max-verem/LensRotaryDecoder/HW/Camera_Lens_Cable/images/pic1.png

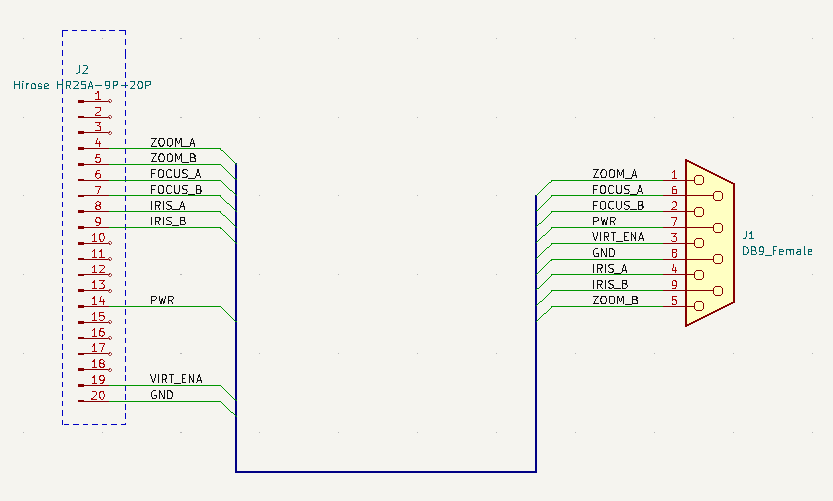
HW/Camera_Lens_Cable/images/pic1.png
