max-verem/LensRotaryDecoder/STM32/Clock_Configuration_16.png

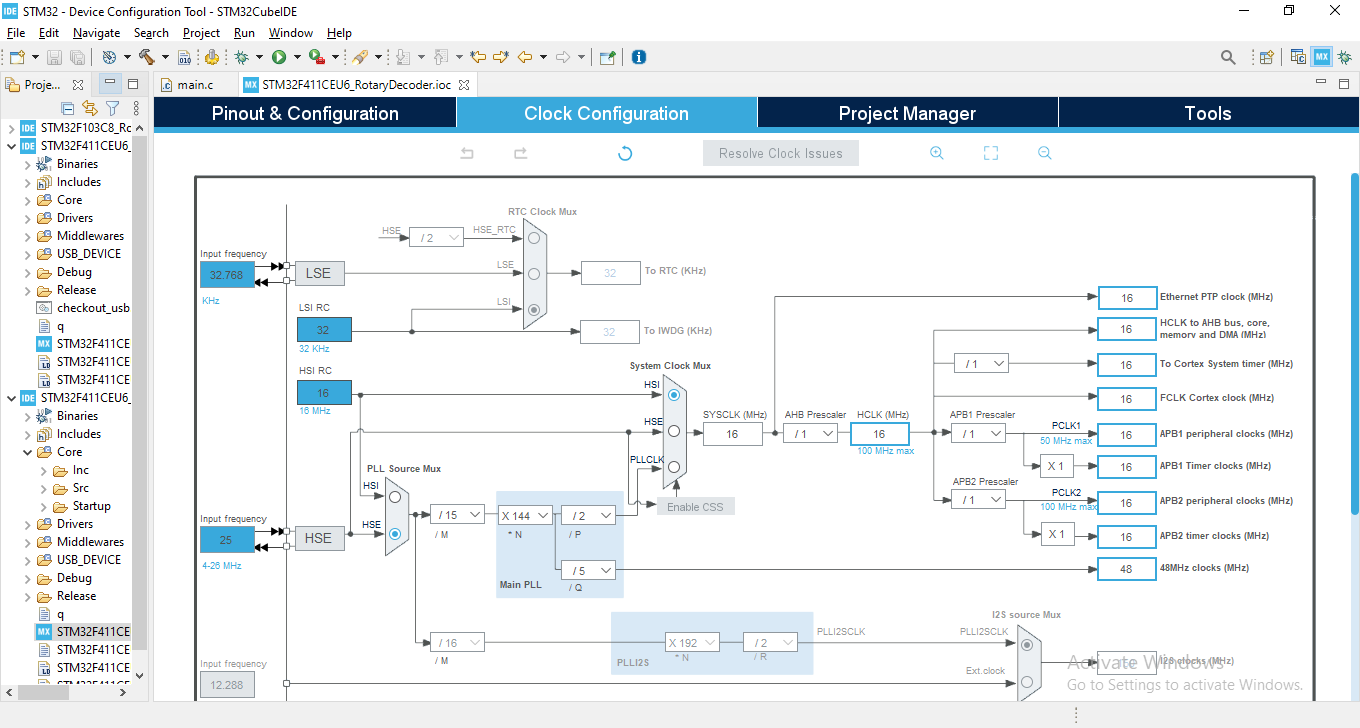
STM32/Clock_Configuration_16.png
