max-verem/LensRotaryDecoder/STM32/STM32F103C8.webp

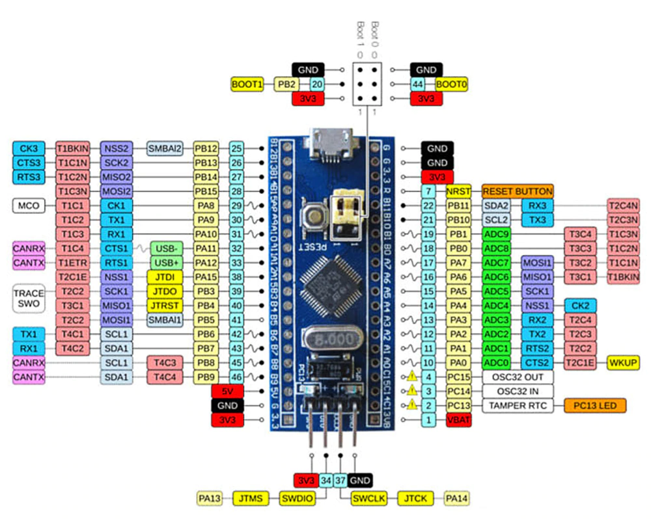
STM32/STM32F103C8.webp
