max-verem/LensRotaryDecoder/STM32/STM32F411CEU6.png

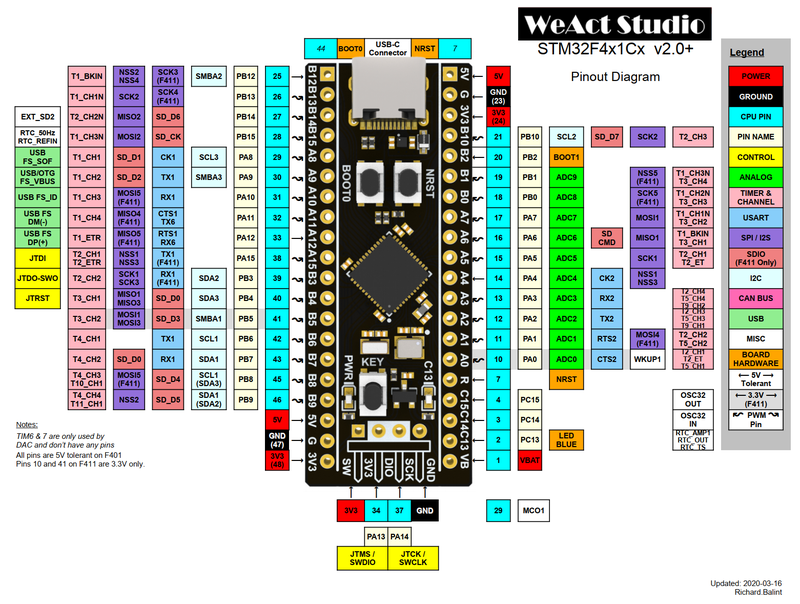
STM32/STM32F411CEU6.png
