max-verem/LensRotaryDecoder/STM32/STM32F411CEU6_FPGA_UART/Core/Inc/main.h

#define LED_PIN_Pin GPIO_PIN_13
#define LED_PIN_GPIO_Port GPIOC
#define W5500_SCS_Pin GPIO_PIN_0
#define W5500_SCS_GPIO_Port GPIOB
#define W5500_RST_Pin GPIO_PIN_1
#define W5500_RST_GPIO_Port GPIOB
