max-verem/LensRotaryDecoder/src/ez-usb/instance.h

#ifndef INSTANCE_H
#define INSTANCE_H

#ifdef __cplusplus
extern "C"
{
#endif /* __cplusplus */

#include <pthread.h>
#include <stdint.h>
#include <limits.h>

#include "ez_usb_rot_dec.git.h"
#include "common/instance.h"

#define PRODUCT_NAME "ez_usb_rot_dec"
#define PRODUCT_STRING PRODUCT_NAME "-" GITVERSION ", Copyright by Maksym Veremeyenko (c) 2022"

#define WS_LISTEN_PORT          8070

#define MAX_TRANSFER_CNT        2048

#define MAX_FREED_TARGETS       8

typedef struct instance_desc
{
    /* lock */
    pthread_mutex_t lock;
    pthread_cond_t cond;

    struct
    {
        int port;
        pthread_t th;
        void* ctx;
//        ws_queue_t main;
        char tmp[PATH_MAX];
    } ws;

    struct
    {
        int queue1_count, queue2_count, errors;
        void *queue1_data[MAX_TRANSFER_CNT], *queue2_data[MAX_TRANSFER_CNT];
    } xfr;

    struct
    {
        int64_t samples, counters[3];
        uint8_t prev[3];
    } decoder;

    struct
    {
        int div, id, trgs;
        uint64_t cnt;
        char targets[MAX_FREED_TARGETS][PATH_MAX];
    } freed;

    DEFAULT_INSTANCE_PARAMS
} instance_t;

int instance_init(instance_t** instance);
int instance_release(instance_t** instance);
int instance_opts(instance_t* instance, int argc, char** argv);
int instance_usage(instance_t* instance);

#ifdef __cplusplus
};
#endif /* __cplusplus */

#endif /* INSTANCE_H */
